FibStack/pi-switcher-plus/software/attiny824_switch_adc_board/attiny824_switch_adc_board/include/twi.h

/*
* Copyright (c) 2021, FibStack
* All rights reserved.
* 
* This source code is licensed under the MIT license found in the
* LICENSE file in the root directory of this source tree. 
*/


#ifndef TWI_H_
#define TWI_H_


#define TWI_BUFFER_SIZE	32

extern char read_buffer[];
extern char write_buffer[];
extern uint8_t bytes_read;
extern uint8_t bytes_written;

extern void TWI0_init(uint8_t address);
extern void TWI0_set_address(uint8_t address);
extern void TWI0_process_interrupt();
extern void TWI0_process_command();


#endif /* TWI_H_ */
